snowman0919/varp-k26-memory-fpga/presentation/final/demo_script.md

# 10-minute run of show

- 0:35 · Slide 1: 정적 큐의 Tail을 줄이는 Work Stealing
- 0:55 · Slide 2: 연구 질문: 지역성과 부하 균형을 함께 얻을 수 있는가
- 1:10 · Slide 3: 연구 대상 구조와 구현 경계
- 1:15 · Slide 4: 지역성 비용을 반영한 Work Stealing
- 1:00 · Slide 5: 실제 Gemma graph에서 평가 작업을 만든다
- 1:05 · Slide 6: 동일 조건에서 S1과 S3의 실행을 비교한다
- 1:20 · Slide 7: 실제 Gemma replay에서도 Tail이 감소했다
- 0:55 · Slide 8: Tail 감소의 비용은 원격 이동이다
- 0:55 · Slide 9: 물리 참조 설계로 다음 검증 범위를 고정했다
- 0:50 · Slide 10: 기여와 한계: 조건부 효과를 규명했다

전체 발표 대본은 [`speaker_notes.md`](speaker_notes.md)에 있다.
