snowman0919/varp-k26-memory-fpga/paper/final/abstract_ko.md

# 국문 초록

온디바이스 소형 언어 모델은 메모리 용량과 가중치 공급 대역폭을 제한된 전력·비용 안에서 함께 해결해야 한다. 본 연구는 Kria K26이 연산·제어를 맡고 외부 Memory FPGA가 다채널 가중치 공급을 맡는 확장형 후보 구조를 설계했다. 실제 Gemma 3 1B 그래프의 7,837개 노드에서 토큰당 183개 투영 연산을 추출하고, 이를 의존성이 있는 802개 출력 타일로 변환해 네 가지 초기 배치와 세 가지 대기열 정책을 비교했다. 합성 불균형 부하에서 지역성 인식 작업 재분배는 정적 배정보다 TileJob p95를 19.13% 줄였지만, Gemma 형상에서는 초기 배치에 따라 p95 변화가 +0.28%에서 −19.79%까지 달라졌다. K26 로컬 메모리 기준선도 외부 6.4 GB/s 후보보다 짧았다. 따라서 외부 8GB와 작업 재분배는 Gemma 1B의 필수 구성요소가 아니라 더 큰 모델·긴 문맥·로컬 경합이 확인될 때 채택할 확장 수단이다. 결과는 제한된 RTL 시뮬레이션과 분석 모델에 근거하며 보드 실측값이 아니다.

**핵심어:** 온디바이스 sLLM, Kria K26, Memory FPGA, 다채널 메모리, 작업 훔치기, SpinalHDL
