snowman0919/varp-k26-memory-fpga/paper/final/code_and_data_availability.md

# 코드와 자료 공개

- 저장소: https://github.com/snowman0919/varp-k26-memory-fpga
- 최종 Release: https://github.com/snowman0919/varp-k26-memory-fpga/releases/tag/v11-conference-final
- 재현 명령: `make test`, `make research-freeze`, `make paper`, `make presentation`

공개 범위에는 SpinalHDL RTL, 실험 설정과 결과 CSV, Gemma 그래프 manifest와 hash,
Figure 생성 소스, KiCad 원본, 논문·발표자료·학습자료가 포함된다. 모델 가중치와
로컬 모델 파일은 라이선스와 용량 때문에 배포하지 않는다.

Release 시점의 commit SHA와 checksum은 최종 공개 인덱스와 Release 본문에 기록한다.
