snowman0919/varp-k26-memory-fpga/paper/technical_report/technical_appendices.md

# 부록 A. 재현 단위와 해석 원칙

본 개정에서 수치의 권위는 그림이 아니라 원본 CSV와 생성 코드에 있다. 직접 확인
자료는 ONNX 그래프의 노드·형상·가중치 구간, KiCad 객체 수처럼 원본에서 다시 셀
수 있는 값이다. RTL 시뮬레이션 자료는 Verilator가 handshake와 순차 논리를 진행해
만든 값이다. 분석 모델 자료는 명시된 작업·자원·비용 식이 만든 값이다. 보드에서
측정한 성능·전력·신호 품질 자료는 없다.

Gemma 작업 목록은 `projection_trace.csv`의 K/N 형상과 연산 순서를 입력으로 삼는다.
원본 가중치는 저장소에 넣지 않으며, 대표 타일만 허가된 로컬 모델에서 추출해 RTL
정확성 fixture로 사용한다. 합성 실험은 같은 부하와 시드의 S1/S2/S3가 같은 작업
목록 해시를 공유해야 유효하다. 재현 검증기는 완료 ID 집합, 중복 완료, timeout,
비용 필드와 manifest 해시를 함께 확인한다.

분석 결과는 보드 실측이나 기능적 언어 모델 추론으로 확대하지 않는다. 특히 p95와
p99는 의존성에서 해제된 TileJob의 완료 지연이다. 32토큰 조건은 동일한 의존성
그래프를 직렬 반복한 것이며, KV cache가 증가하는 실제 텍스트 생성은 아니다.

# 부록 B. 폐루프 논리 RTL 구조

`ClosedLoopVirtualPrototypeTop`은 작업 수락, DMA 요청 FIFO, 다중 채널 스케줄러,
DDR 응답 경계, 논리 링크 FIFO, job ID 결합, 대기열 정책, MatVec 결과를 하나의
역할 흐름으로 연결한다. 메모리 응답이 들어오기 전에는 연산 명령을 만들 수 없고,
같은 응답은 한 번만 수락된다. 기존 `K26WorkStealingTop`의 스케줄러·메모리·링크
평면은 독립적인 구조 실험으로 남겨 두고, 새 top을 폐루프 논리 검증 경로로 쓴다.

대표 검증은 Gemma의 `gate_proj`, `lm_head`, `o_proj`에서 추출한 16×4 INT8 타일
세 개를 사용한다. 각 타일은 작업 수락→DMA 요청→메모리 응답→MatVec 결과 순서를
지켰고 결과는 소프트웨어 INT32 내적과 일치했다. 수락/요청/응답/결과 사이클은
각각 5/11/13/88, 89/95/97/172, 173/179/181/256이다. 이 범위는 실제 가중치가
논리 데이터 경로를 통과했다는 사실만 확인한다.

GTH 직렬화, 레인 결합, CDC, 패킷 분할, CRC 재전송, 크레딧 반환은 구현되지 않았다.
DDR 응답은 MIG 경계에서 주입하므로 DDR3L PHY와 보정도 검증하지 않았다. 따라서
논리 링크 폭과 FIFO 깊이는 구조 사실이지만 Fmax, 물리 대역폭, 보드 처리율은 아직
말할 수 없다.

# 부록 C. Gemma 투영에서 TileJob으로의 변환

Gemma 3 1B ONNX 그래프는 7,837개 노드와 183개 dense 투영을 토큰마다 가진다.
Attention의 q/k/v/o가 104개, MLP의 gate/up/down이 78개, lm_head가 1개다. 원본
float32 투영 가중치는 약 4.0 GiB이고 명시적 INT8 변환 뒤 약 1.0 GiB로 모델링한다.

개정 모델은 투영 하나를 작업 하나로 두지 않는다. 각 투영의 전체 K차원을 유지하고
N≤1024인 출력 구간으로 나누어 토큰당 802개 TileJob을 만든다. q/k/v→o,
o→gate/up, gate/up→down, down→다음 계층의 보수적 장벽을 둔다. 다음 토큰은
현재 토큰의 lm_head가 끝난 뒤에만 열린다. 따라서 32토큰은 25,664개 TileJob의
직렬 의존성 반복이다.

초기 배치는 네 가지다. 기존 산술 규칙은 C0/C1/C2/C3에 464/208/78/52개 타일을
둔다. 라운드로빈은 201/201/200/200개로 나눈다. 크기 균형은 누적 MAC이 작은
클러스터에 다음 작업을 둬 198/202/200/202개가 된다. 채널 친화는 가중치 채널과
같은 번호의 클러스터를 우선해 394/136/136/136개가 된다. 이 네 배치는 실제
컴파일러 결과가 아니라 설계 민감도 변수다.

# 부록 D. 정책과 원격 복사 비용

S1은 자기 대기열만 선착순으로 처리하는 정적 다중 대기열이다. S2는 유휴
클러스터가 다른 대기열의 가장 오래된 작업을 가져온다. S3는 예상 대기 감소에서
가중치·활성값·부분합 이동과 링크 불일치 비용을 뺀 점수가 양수일 때만 가져온다.

작업 이동은 단순 ownership counter가 아니다. 모델은 정적 배치의 선호 링크로
가중치를 먼저 공급한 뒤, 실행 클러스터가 바뀌면 가중치·활성값·부분합의 추가
바이트를 새 링크로 복사한다. 기본 링크 서비스와 추가 복사 서비스의 바이트·사이클을
별도 필드로 보존하고, 두 서비스 모두 완료시간 계산에 들어간다. 따라서 S3가
S2보다 작은 원격 작업을 골라 비지역 가중치를 줄일 수 있어도 S1보다 느릴 수 있다.

의존성 있는 작업은 모든 선행 작업이 끝나야 대기열에 들어간다. TileJob 지연의
시작점은 원래 생성 시각이 아니라 의존성 해제 시각이다. 이 정의는 단계 장벽 때문에
기다린 시간을 스케줄러 지연으로 잘못 세지 않는다.

# 부록 E. 합성 부하의 동일 시드 쌍비교

분석 모델 기본값은 클러스터 4개, 메모리 채널 4개, 논리 링크 묶음 4개, 묶음당
128비트다. 각 합성 부하는 1,000개 작업이며 시드 다섯 개를 사용한다. 정책별
중앙값을 먼저 비교하지 않고, 같은 시드의 S3/S1 또는 S3/S2 변화율을 계산한 뒤
그 변화율의 중앙값을 보고한다.

균형 부하에서 S3와 S1의 완료시간·p95·p99 차이는 모두 0%다. 채널 집중 부하도
p95와 p99 차이가 0%이며 완료시간만 −0.06%다. 순간 집중 부하는 p95 −0.08%,
p99 −1.16%로 효과가 작다. 이 조건들은 연산 클러스터의 빈 시간이 이동 비용을
상쇄할 만큼 크지 않다.

혼합 부하에서는 S3가 S1보다 완료시간 15.91%, p95 17.70%, p99 16.92% 짧다.
편향 부하에서는 각각 17.25%, 19.13%, 18.71% 짧다. 같은 편향 부하의 S2와
비교하면 S3의 비지역 가중치가 35.49% 적고 완료시간 차이는 +0.01%로 거의 같다.
즉, 지역성 인식은 가장 오래된 작업을 무조건 가져오는 것보다 전송량을 줄이지만,
그 자체가 언제나 추가 완료시간 이득을 주는 것은 아니다.

다섯 시드는 제한된 민감도이며 통계적 모집단을 대표하지 않는다. 신뢰구간이나
유의확률을 제시하지 않고 중앙값과 조건별 방향만 해석한다. 이 합성 수치는 Gemma
실행 성능으로 옮겨 읽지 않는다.

# 부록 F. Gemma 형상의 초기 배치 민감도

기존 산술 배치에서 S3는 S1보다 완료시간이 4.80% 길고 TileJob p95도 0.28%
길다. 추가 링크 이동량은 토큰당 395.2 MB다. 라운드로빈에서는 완료시간이 0.59%
짧고 p95 변화는 없으며 추가 이동량은 43.3 MB다. 크기 균형에서는 완료시간이
0.76% 짧고 p95 변화는 없으며 추가 이동량은 110.8 MB다.

채널 친화 배치에는 큰 작업 쏠림이 남아 있다. 이 조건에서 S3는 완료시간을 7.56%,
TileJob p95를 19.79% 줄이지만 추가 이동량은 토큰당 416.4 MB다. 결과는 “S3가
항상 빠르다”가 아니라 “초기 배치 뒤 남은 불균형이 이동 비용보다 클 때만 효과가
있다”를 지지한다. 실제 컴파일러 배치가 확보되면 네 민감도 중 어느 조건과 가까운지
다시 확인해야 한다.

# 부록 G. K26 로컬과 외부 메모리 후보

용량 모델은 INT8 가중치, 문맥 길이 32K의 KV cache, 활성값과 실행 여유분을 합해
2.43 GiB를 얻는다. 이는 명목 K26 4GB 안에 들어간다. 따라서 외부 8GB는 Gemma
1B 용량에 반드시 필요한 구성이 아니다.

크기 균형 S1에서 K26 로컬 유효 대역폭 4.8/9.6/14.4 GB/s의 완료시간은
45.0M/24.6M/17.8M 사이클이다. 외부 네 채널 합계 3.2/6.4/12.8 GB/s 후보는
238.3M/120.6M/62.4M 사이클이다. 외부 6.4 GB/s에서 링크 폭을 64비트에서
256비트로 넓혀도 결과가 거의 같아 메모리 공급이 병목임을 보인다.

이 값들은 실측치가 아니라 채택 임계값을 탐색하는 분석 입력이다. 시험한 범위에서는
외부 후보가 K26 로컬 기준선을 이기지 못했다. 외부 Memory FPGA의 다음 평가 조건은
3B 이상 모델, 더 긴 문맥, K26 로컬 경합, 독립 공급 경로가 필요한 다중 클러스터다.
전체 BOM과 보드 전력이 없으므로 저비용·저전력 달성을 주장하지 않는다.

# 부록 H. KiCad 라우팅 쿠폰의 실제 범위

KiCad 자료는 K26 모듈과 Memory FPGA가 실장된 전체 보드가 아니다. J1/J2의 일반
경계 커넥터, MLCC, 단일 DDR3L 메모리 slice와 일부 GTH·기준 클록 배선을 둔 축소
라우팅 쿠폰이다. 화면의 3D 렌더는 객체와 배선 위치를 설명할 뿐 제작 준비 상태를
보여 주지 않는다.

원본에는 footprint 29개가 있고 GTH·기준 클록 관련 단일 종단 net 20개가 명시적으로
라우팅되어 있다. 제한된 규칙에서 ERC/DRC 0이라는 결과는 쿠폰 subset에만 적용된다.
전체 설계의 핀 지정, 전원 트리, 네 DDR controller, K26 실제 커넥터, FPGA package,
MIG 배치, 전체 라우팅과 제조 검증은 닫히지 않았다.

후속 단계는 정확한 MPN과 데이터시트, K26 커넥터 pinout, FPGA transceiver quad,
MIG bank, stackup, 임피던스·손실·지터 예산, plane·stitching, PDN/SI/thermal/EMC,
제조 검사점을 요구한다. 그전에는 `NOT FOR FABRICATION` 표시를 유지한다.

# 부록 I. 빌드와 품질 관문

논문 빌드는 Markdown을 독립 HTML로 변환하고 SVG를 포함한 뒤 headless Chromium으로
PDF를 출력한다. 제출 원고는 A4 2단, 기술보고서는 A4 1단이다. 빌드 뒤 페이지 수,
텍스트 추출, 금지 주장, Figure 순서와 출처를 검사한다. SVG의 원본 글꼴과 최종 PDF
제목 글꼴의 비율로 최종 최소 글꼴을 보수적으로 계산하며 8pt 미만이면 실패한다.

재현 순서는 합성 실험, 의존성 인식 Gemma 실험, K26 로컬/외부 민감도, RTL 테스트,
논문 빌드다. 허가된 원본 Gemma 경로가 없더라도 저장된 trace와 대표 fixture로
핵심 검증을 반복할 수 있다. 모델 원본 가중치는 저장소와 release에 포함하지 않는다.

최종 해석은 세 문장으로 제한된다. 첫째, Gemma 1B에는 K26 로컬 구성이 우선이다.
둘째, 외부 메모리는 더 큰 모델·긴 문맥·로컬 경합이 확인될 때 다시 평가한다. 셋째,
Work Stealing은 초기 배치가 남긴 불균형이 이동 비용보다 클 때만 켠다.
