snowman0919/varp-k26-memory-fpga/presentation/final/assets/bottleneck_migration_frame.png

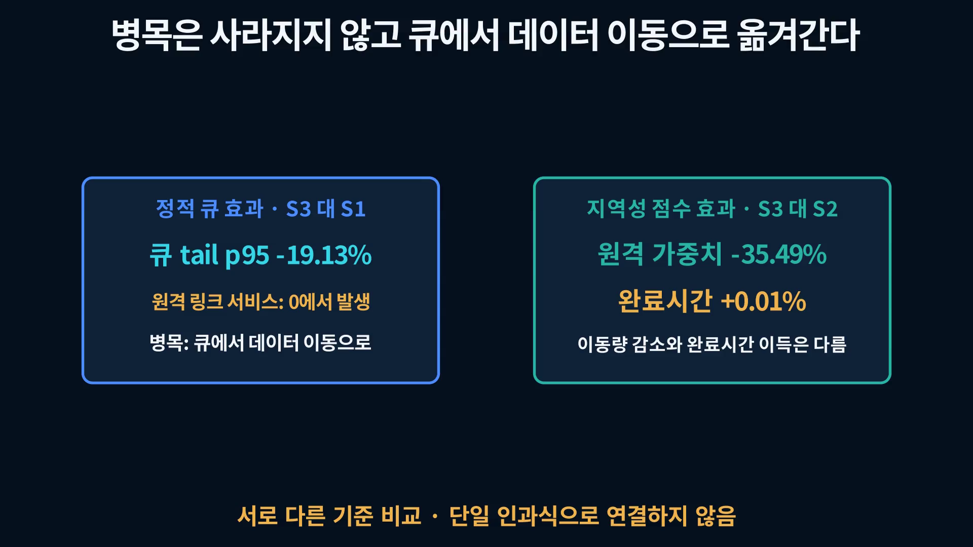
presentation/final/assets/bottleneck_migration_frame.png
