snowman0919/varp-k26-memory-fpga/presentation/final/assets/bottleneck_shift.png

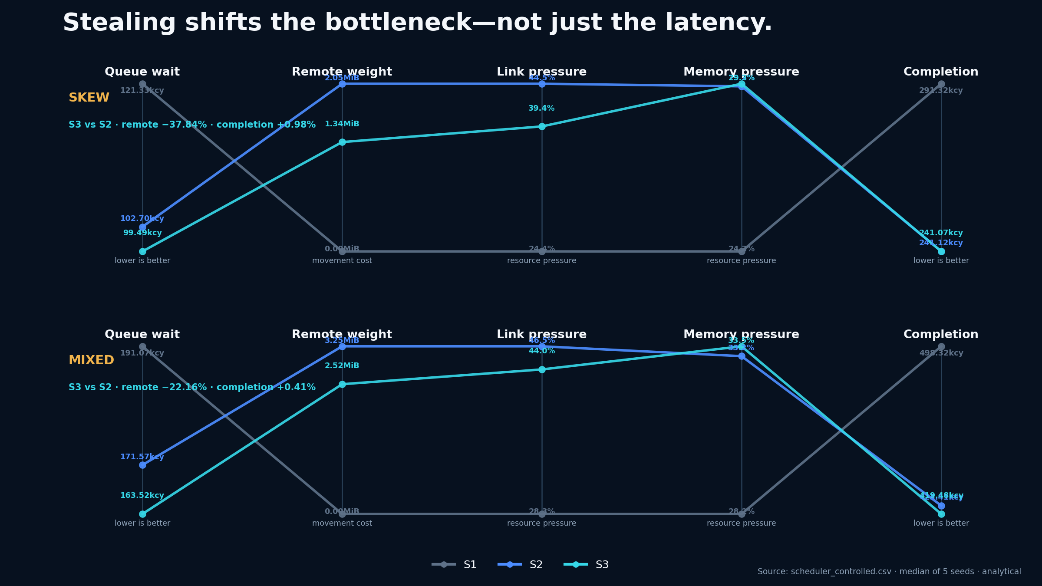
presentation/final/assets/bottleneck_shift.png
