snowman0919/varp-k26-memory-fpga/presentation/final/assets/kicad_link_crop.png

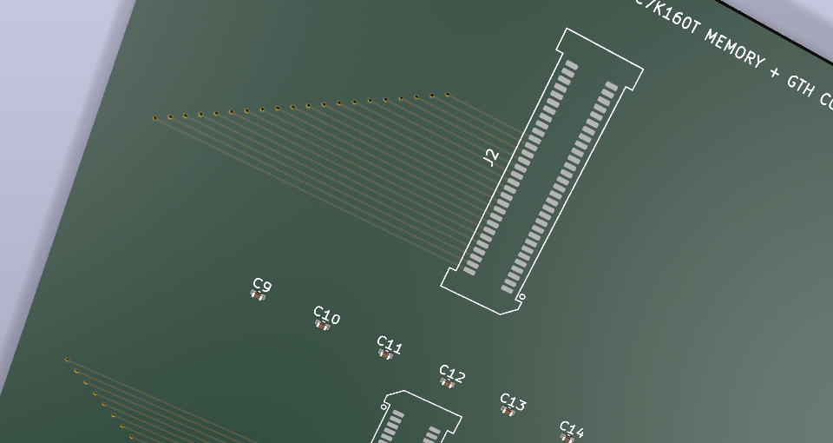
presentation/final/assets/kicad_link_crop.png
