snowman0919/varp-k26-memory-fpga/presentation/final/assets/kicad_refclk_crop.png

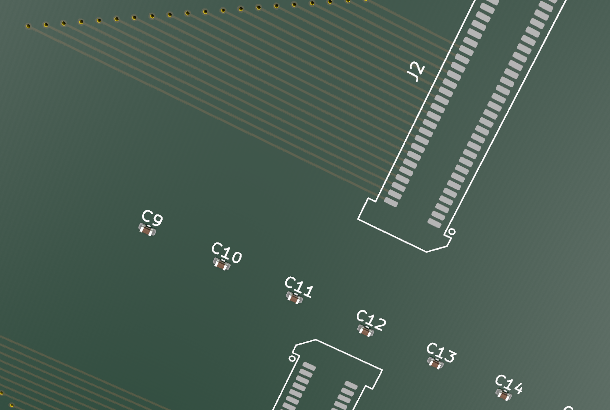
presentation/final/assets/kicad_refclk_crop.png
