snowman0919/varp-k26-memory-fpga/presentation/final/assets/kicad_top_render.png

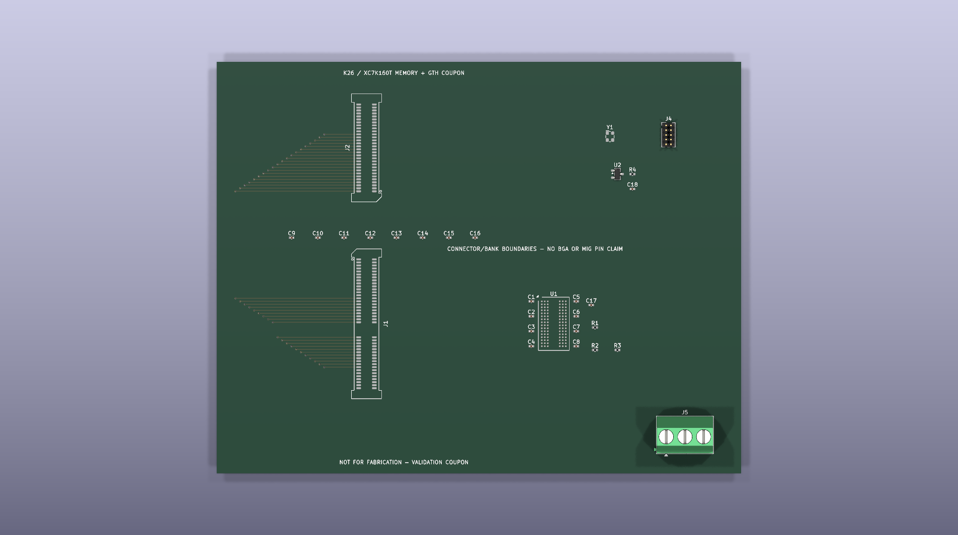
presentation/final/assets/kicad_top_render.png
