snowman0919/varp-k26-memory-fpga/presentation/final/assets/tile_dataflow_frame.png

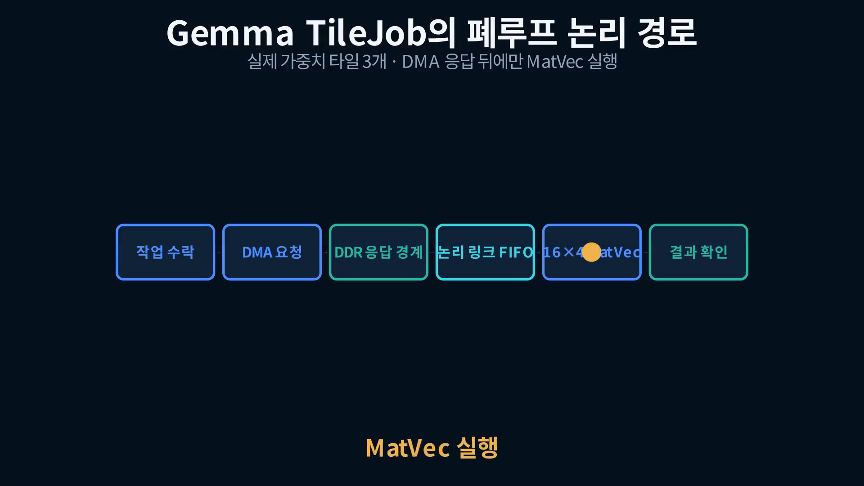
presentation/final/assets/tile_dataflow_frame.png
