snowman0919/varp-k26-memory-fpga/presentation/final/assets/work_stealing_storyboard.png

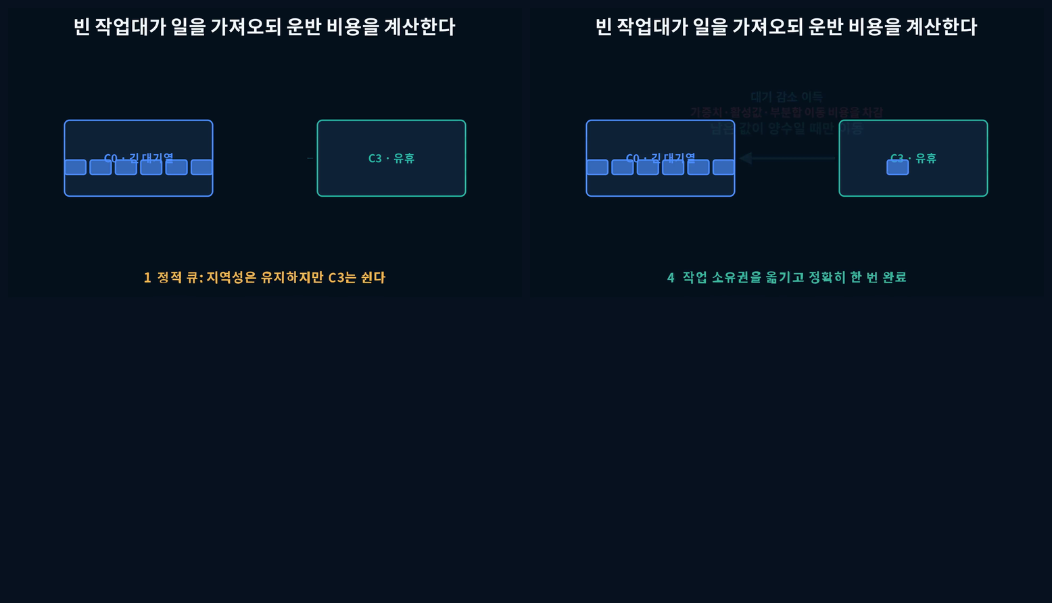
presentation/final/assets/work_stealing_storyboard.png
