snowman0919/varp-k26-memory-fpga/presentation/final/slide_contact_sheet.png

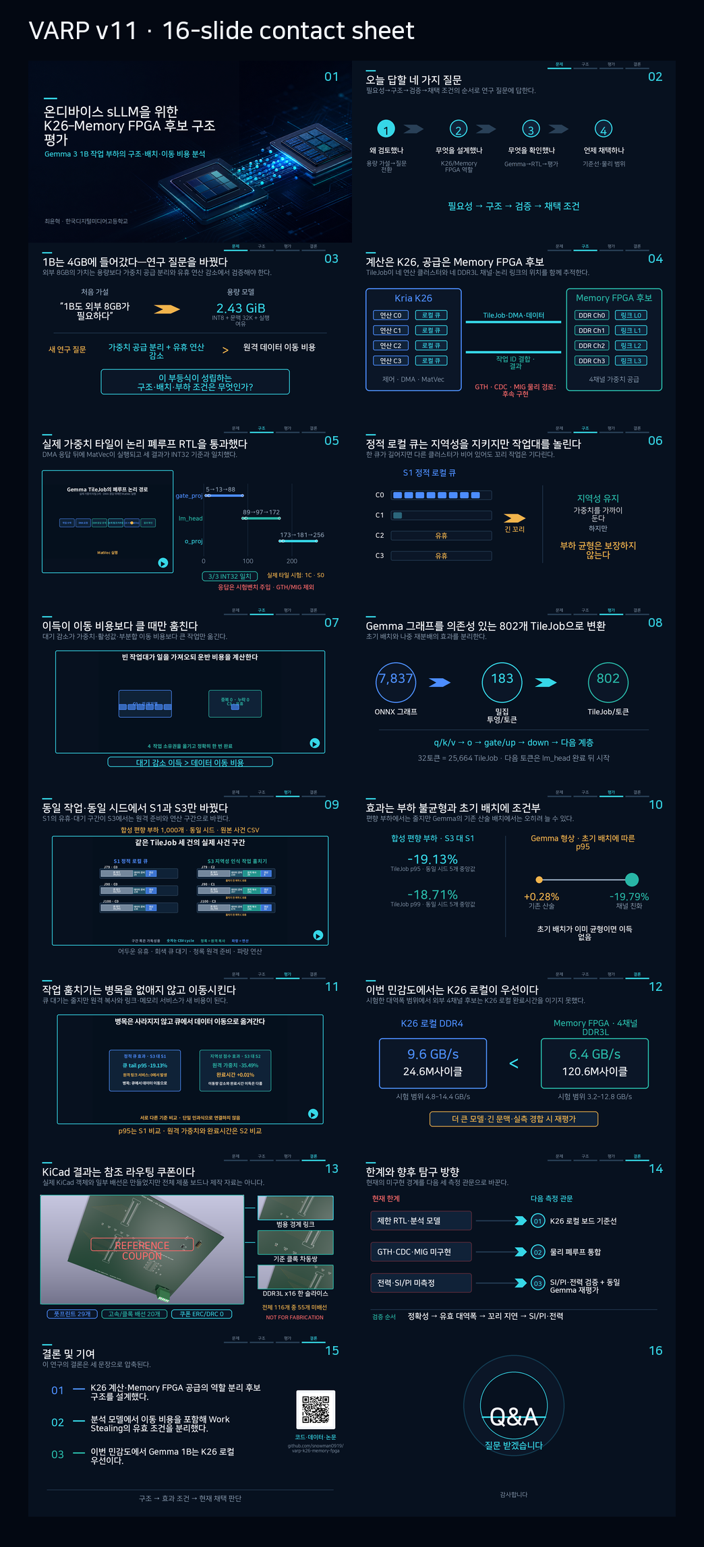
presentation/final/slide_contact_sheet.png
