snowman0919/varp-k26-memory-fpga/presentation/final/slides/slide_04.png

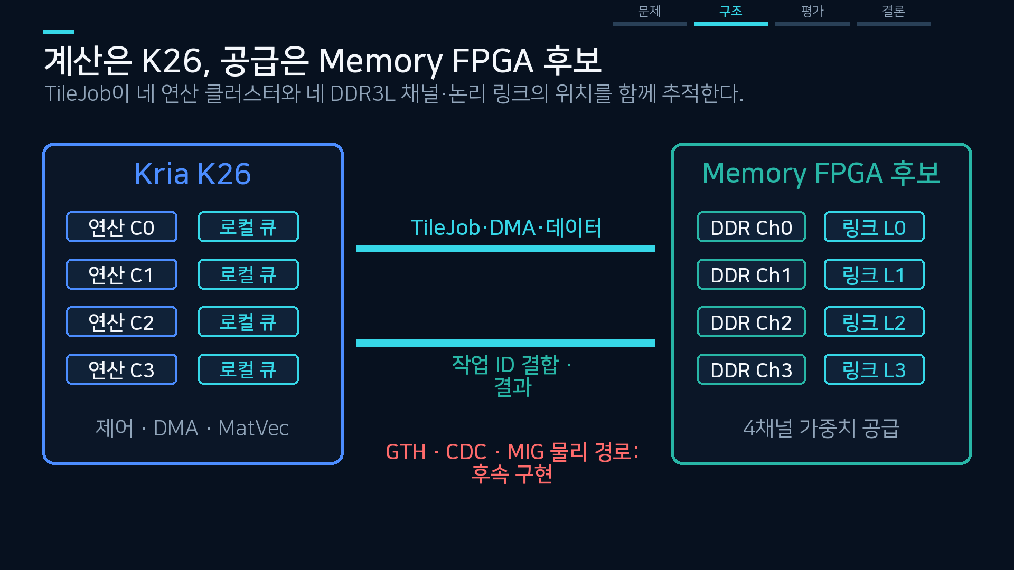
presentation/final/slides/slide_04.png
