snowman0919/varp-k26-memory-fpga/results/capacity/memory_scaling_options.csv

option | capacity_gib_binary | capacity_gb_decimal | channels | data_width_per_channel_bits | ranks_per_channel | 8gbit_x8_dies_per_channel | total_8gbit_x8_packages | physical_4gbit_die_count | component_reference | component_lifecycle | component_status | package_internal_organization | pin_rate_ceiling_mts | aggregate_pin_rate_ceiling_gbs | bandwidth_effect_of_second_rank | implementation_status | evidence_type
8GB_4ch_x16 | 8 | 8.590 | 4 | 16 | 1 | 2 | 8 | 16 | AS4C1G8D3LA-10BCN | current manufacturer catalog; distributor Active at DigiKey | cost-model candidate; MIG qualification unresolved | two_4gbit_x4_dies_stacked_as_one_x8_rank | 800 | 6.400 | capacity_only; no added channel bandwidth | blocked_missing_Vivado_MIG_placement_timing | datasheet-plus-capacity-arithmetic
16GB_4ch_x16 | 16 | 17.180 | 4 | 16 | 2 | 4 | 16 | 32 | AS4C1G8D3LA-10BCN | current manufacturer catalog; distributor Active at DigiKey | cost-model candidate; MIG qualification unresolved | two_4gbit_x4_dies_stacked_as_one_x8_rank | 800 | 6.400 | capacity_only; no added channel bandwidth | blocked_missing_Vivado_MIG_placement_timing | datasheet-plus-capacity-arithmetic
