snowman0919/varp-k26-memory-fpga/experiments/gemma3_1b/representative_weight_tiles_int8.csv

projection_class | k_index | activation_int8 | weight_n0_int8 | weight_n1_int8 | weight_n2_int8 | weight_n3_int8 | reference_n0_int32 | reference_n1_int32 | reference_n2_int32 | reference_n3_int32 | quantized_tile_sha256
o_proj | 0 | -124 | -32 | 72 | -9 | 34 | 3783 | 19577 | -11581 | -7508 | a2136798e7f3979e2c3ad1799ae2a2b4499c9ec8827946a7bd8c5a9e25218ccb
o_proj | 1 | -107 | 44 | -23 | 26 | 42 | 3783 | 19577 | -11581 | -7508 | a2136798e7f3979e2c3ad1799ae2a2b4499c9ec8827946a7bd8c5a9e25218ccb
o_proj | 2 | -90 | 23 | -58 | -123 | -66 | 3783 | 19577 | -11581 | -7508 | a2136798e7f3979e2c3ad1799ae2a2b4499c9ec8827946a7bd8c5a9e25218ccb
o_proj | 3 | -73 | -20 | -39 | -23 | -1 | 3783 | 19577 | -11581 | -7508 | a2136798e7f3979e2c3ad1799ae2a2b4499c9ec8827946a7bd8c5a9e25218ccb
o_proj | 4 | -56 | -50 | -15 | 39 | 0 | 3783 | 19577 | -11581 | -7508 | a2136798e7f3979e2c3ad1799ae2a2b4499c9ec8827946a7bd8c5a9e25218ccb
o_proj | 5 | -39 | 127 | 14 | -19 | 9 | 3783 | 19577 | -11581 | -7508 | a2136798e7f3979e2c3ad1799ae2a2b4499c9ec8827946a7bd8c5a9e25218ccb
o_proj | 6 | -22 | -40 | -3 | 24 | -18 | 3783 | 19577 | -11581 | -7508 | a2136798e7f3979e2c3ad1799ae2a2b4499c9ec8827946a7bd8c5a9e25218ccb
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
