snowman0919/varp-k26-memory-fpga/experiments/gemma3_1b/scheduler_replay.csv

schema_version | evidence_type | scheduler | workload | seed | process_repetition | clusters | channels | bundles | link_width_bits | service_overlap_mode | jobs | ledger_sha256 | completed_jobs | total_completion_cycles | throughput_jobs_per_kcycle | mean_tile_latency_cycles | p50_tile_latency_cycles | p95_tile_latency_cycles | p99_tile_latency_cycles | cluster_utilization_mean | cluster_compute_utilization_mean | cluster_reservation_occupancy_mean | cluster_idle_cycles | cluster_compute_idle_cycles | queue_wait_mean_cycles | max_queue_depth | queue_imbalance | ingress_backlog_final | steal_attempts | successful_steals | steal_success_rate | remote_weight_bytes | activation_retransmission_bytes | partial_sum_traffic_bytes | link_bundle_utilization_mean | ddr_channel_utilization_mean | request_serializer_wait | request_credit_wait | request_cdc_wait | outstanding_table_full_wait | response_serializer_wait | response_cdc_wait | consumer_fifo_full_wait | bundle_contention_wait | memory_command_wait | central_queue_control_cycles | oracle_resource_lower_bound_cycles | oracle_schedule_kind | starvation_ratio | completion_reordered | timed_out | correctness | input_job_id_count |
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
