snowman0919/varp-k26-memory-fpga/presentation/final/assets/kicad_validation_scope_inset.png

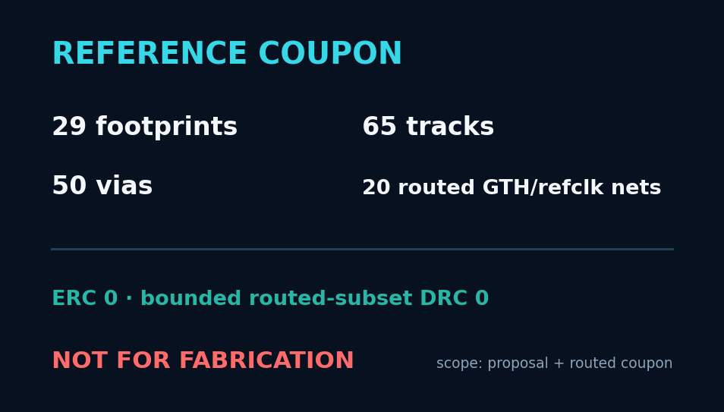
presentation/final/assets/kicad_validation_scope_inset.png
