snowman0919/varp-k26-memory-fpga/presentation/final/assets/tail_latency_results_frame.png

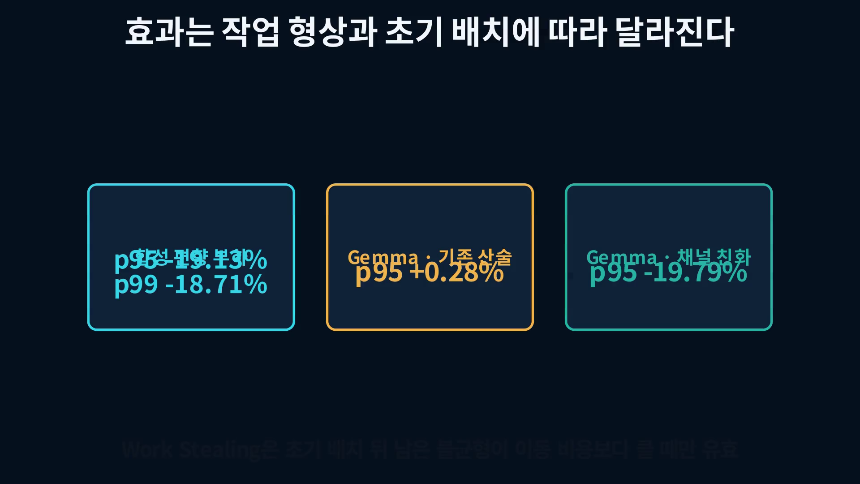
presentation/final/assets/tail_latency_results_frame.png
