snowman0919/varp-k26-memory-fpga/paper/revisions/v11-r1/change_log.md

# v11-r1 변경 기록

- v10 제출본을 v11 개정의 거절 기준선으로 보존했다.
- 외부 가속기 필요성, 닫힌 데이터 경로, 비용·전력, KiCad 범위를 Critical로 등록했다.
- 이 버전의 성능 수치와 결론은 후속 v11 원고에서 사용하지 않는다.
