snowman0919/varp-k26-memory-fpga/paper/revisions/v11-r4/review.md

# Review 4 — 하드웨어 주장 경계와 물리 시각자료

판정: **PASS**

독립 검토자는 RTL, 분석 모델, KiCad 쿠폰과 발표 화면의 연결을 점검했다. 실제
Gemma 타일 시험은 1클러스터·1채널·S0이며 시험벤치 응답을 사용한다는 점, 물리
GTH·CDC·크레딧·MIG 경로는 열려 있다는 점, 외부 8 GiB는 분석 후보라는 점이
논문·발표·Q&A에서 일관됨을 확인했다.

Q&A의 표 번호, 6.4/12.8 GB/s 비교 경계, 메모리 조직 후보, 실제 RTL 파일 경로를
현재 자료에 맞게 고쳤다. 최종 검토에서 누락 경로와 하드웨어 과장 표현은 0건이다.
