snowman0919/varp-k26-memory-fpga/paper/revisions/v11-final/review.md

# v11 최종 독립 검토 종합

판정: **PASS**

다섯 차례의 지정 검토와 추가 최종 언어 검토를 마쳤다.

| 검토 | 초점 | 최초 판정 | 최종 상태 |
|---|---|---|---|
| Review 1 | 가속기 구조 기여 | FAIL | K26 로컬 기준선·닫힌 논리 경로·시스템 중심 서술 반영 |
| Review 2 | 실험 인과와 공정성 | FAIL | 의존성·원격 서비스 비용·초기 배치 민감도 반영 |
| Review 3 | 한국어 가독성 | FAIL | 논문·Q&A·발표자 노트 전면 교정 |
| Review 4 | 하드웨어 주장·시각자료 | FAIL | 포인터와 물리 경계 수정 후 PASS |
| Review 5 | 컨퍼런스 발표·심사 대응 | FAIL | Slide 7·9와 Q&A 수정 후 PASS |
| 추가 최종 검토 | 언어·추적성 | FAIL | 지정 표현 12건 수정 후 PASS |

최종 Q&A는 89문항이며 모든 경로형 근거가 존재한다. 제출 논문은 8쪽, 최소 그림
글꼴 8.102pt, 발표는 14장·목표 580초·내장 영상 4개다. 논문 PDF, 발표 PNG와
스터디팩 PDF에서 한글 대체 문자, 글자 겹침과 화면 밖 요소를 발견하지 않았다.
