snowman0919/varp-k26-memory-fpga/paper/revisions/v11-r2/review.md

# Review 2 — 실험 인과성과 지표 정의

판정: **FAIL → 수정 반영 후 조건부 통과**

독립 검토자는 v10 실험이 원격 전송량을 사후 집계했을 뿐 실행시간에 비용으로
부과하지 않았고, 32-token 조건에서 계층·토큰 의존성을 지키지 않았으며, p95와
p99가 사용자 요청 지연이 아니라 TileJob 지연이라는 점을 지적했다. 또한 초기
배치 한 종류만으로 Work Stealing의 효과를 일반화할 수 없다고 판단했다.

## Critical

1. 원격 가중치 이동이 링크·메모리 서비스 시간에 들어가지 않았다.
2. 토큰과 투영 단계가 겹쳐 autoregressive decode의 의존성을 위반했다.
3. 초기 배치가 편향된 산술 규칙 하나뿐이었다.
4. p95·p99의 모집단과 지연 시작 시점이 불명확했다.
5. 동일 seed를 짝지은 정책 효과가 보고되지 않았다.

## 반영한 수정

- 원격 가중치·활성값·부분합의 추가 바이트와 서비스 사이클을 실행시간에 직접
  부과했다.
- q/k/v→o→gate/up→down 장벽과 토큰 직렬화를 추가했다.
- 기존 산술, 라운드로빈, 크기 균형, 채널 친화의 네 초기 배치를 비교했다.
- p95·p99를 의존성 해제 시점부터 완료까지의 TileJob 지연으로 한정했다.
- 같은 작업·seed를 공유하는 S1/S2/S3 결과의 paired median을 계산했다.

수정 뒤 재실험은 정책 효과가 초기 배치와 이동 비용에 조건부임을 보여 준다.
따라서 원고는 “Gemma 요청 tail 개선”을 주장하지 않고 TileJob 수준의 분석으로
범위를 제한한다.
