snowman0919/varp-k26-memory-fpga/paper/revisions/v11-r3/change_log.md

# v11-r3 변경 기록

- 한국어 본문의 불필요한 영문 일반 용어를 자연스러운 한국어로 바꿨다.
- 합성 부하 이름과 K26 로컬 표기를 통일했다.
- 그림 2의 단계 라벨, 그림 3의 하단 설명, 그림 4의 근접 이벤트 라벨이 겹치지
  않도록 다시 배치했다.
- 그림 4는 개별 근접 이벤트 네 개를 한 문장형 사건 묶음으로 바꾸고 3/3 결과
  일치 badge를 하나로 통합했다.
- 원고 PDF 8쪽, Figure 최소 글꼴 8.102pt, 텍스트·배치 검증을 통과했다.
