snowman0919/varp-k26-memory-fpga/paper/revisions/v11-r3/review.md

# Review 3 — 한국어 가독성과 발표 적합성

판정: **FAIL → 수정 반영 후 조건부 통과**

독립 검토자는 기존 원고가 내부 검증 보고서처럼 읽히고, 영문 용어가 문장 안에
과도하게 섞이며, 독자가 설계 질문보다 증거 분류를 먼저 만나게 된다고 지적했다.
발표자 노트 역시 말로 전달하기 어려운 문장 구조였으며 README는 영어 중심이었다.

## 반영한 수정

- 원고의 전개를 문제→설계 목표→후보 구조→Gemma 매핑→정책→실험→결정→한계
  순서로 정리했다.
- lane bonding, packet, credit, compiler, activation, seed, hash, cycle 등의
  일반 용어를 한국어로 바꾸고 고유 기술명만 영어로 유지했다.
- balanced/skew/hotspot/bursty/mixed를 균형/편향/채널 집중/순간 집중/혼합으로
  통일했다.
- “증거 경계”를 주제에서 제거하고, 직접 확인·RTL 시뮬레이션·분석 모델·미검증의
  구분은 해석에 필요한 한 표와 한계 절에만 남겼다.
- Figure 내부 문구의 영문과 축약을 줄이고 최종 PDF 최소 글꼴 8pt를 유지했다.

README와 발표자 노트의 구어체 전환은 발표자료 개정 단계에서 계속 검토한다.
