snowman0919/varp-k26-memory-fpga/paper/revisions/v11-r5/change_log.md

# v11-r5 변경 기록

- Slide 7 제목을 한 줄로 줄이고 영상 영역과 하단 판단식을 분리했다.
- Slide 9의 J79/J90/J100 라벨 위치를 원본 사건 구간 안에서 읽히도록 옮겼다.
- 발표자 노트의 내부 영문을 한국어 발표 문장으로 바꿨다.
- 현재 논문 절 제목과 표 번호에 맞춰 89개 Q&A 포인터를 갱신했다.
- PPTX의 4개 영상을 직접 포함하고 PDF·PNG·contact sheet를 같은 빌드로 맞췄다.
