snowman0919/varp-k26-memory-fpga/paper/revisions/v11-r5/review.md

# Review 5 — 학술 발표 화면과 Q&A

판정: **PASS**

독립 검토자는 14개 슬라이드 PNG를 100% 크기로 확인하고 PPTX, PDF, 내장 영상,
발표자 노트와 Q&A의 일관성을 점검했다. Slide 7의 제목·결론·영상·하단 수식과
Slide 9의 J79/J90/J100 라벨이 겹치지 않으며, 한 슬라이드 한 메시지 원칙을
충족한다.

최종 발표는 14장, 내장 Manim 영상 4개, 발표자 노트 14개, 목표 580초이며 읽기
추정은 574.3초다. 연구 질문→구조→검증→조건부 결과→채택 판단의 학술 발표
흐름을 유지한다.
